GreenShoeGarage/HackerRadio/Software/HackerRadio_Firmware/data/images/gsg.jpg

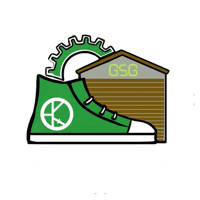
Software/HackerRadio_Firmware/data/images/gsg.jpg
