GreenShoeGarage/HackerRadio/Software/HackerRadio_Firmware/secrets_example.h

//Save me as secrets.h
//Change ifnded and define statements below to secrets_h

#ifndef secrets_example_h
#define secrets_example_h

const char *ssid = "hackerradio"; // The name of the Wi-Fi network that will be created
const char *password = "changeme";   // The password required to connect to it, leave blank for an open network

#endif
